CASE-Association/FolkraceCar/img/Stream/img1.jpg

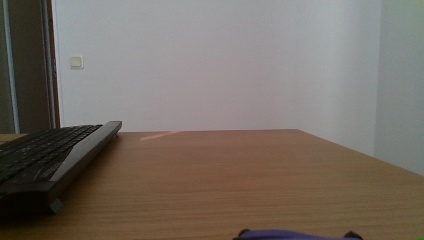
img/Stream/img1.jpg
