CASE-Association/FolkraceCar/img/Stream/img2.jpg

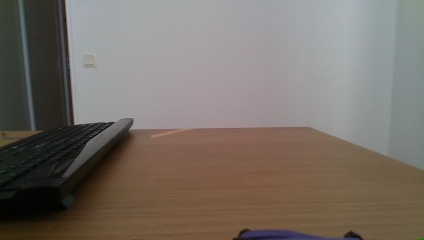
img/Stream/img2.jpg
