CASE-Association/FolkraceCar/img/Stream/img3.jpg

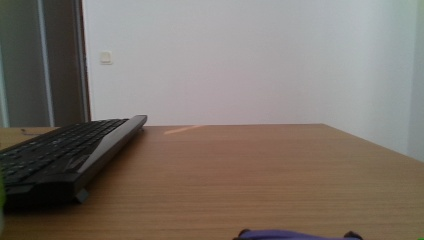
img/Stream/img3.jpg
