CASE-Association/FolkraceCar/img/Stream/img4.jpg

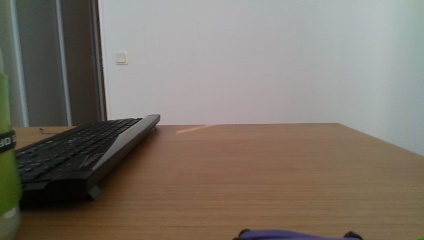
img/Stream/img4.jpg
