CASE-Association/FolkraceCar/img/Stream/img5.jpg

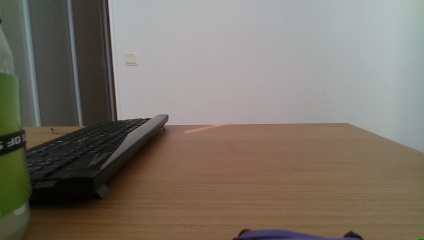
img/Stream/img5.jpg
