CASE-Association/FolkraceCar/img/Stream/img6.jpg

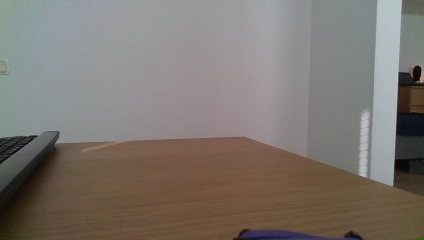
img/Stream/img6.jpg
