CASE-Association/FolkraceCar/img/Stream/img7.jpg

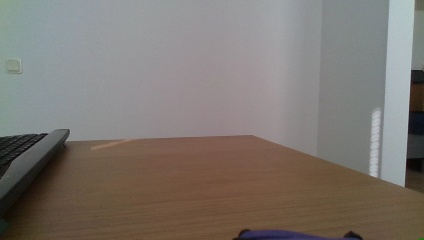
img/Stream/img7.jpg
