CASE-Association/FolkraceCar/img/Stream/img8.jpg

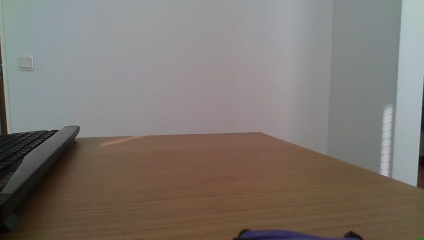
img/Stream/img8.jpg
