CASE-Association/FolkraceCar/img/Stream/img9.jpg

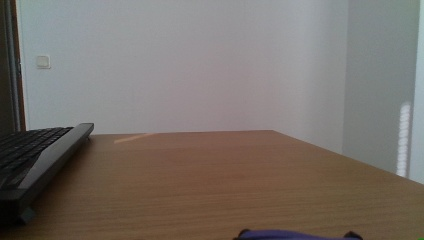
img/Stream/img9.jpg
