CASE-Association/FolkraceCar/software/module/pathplanner.py

from numpy.linalg import svd, det
import multiprocessing as mp
from module.camera import *
import numpy as np
from threading import Thread
import module.config as conf


class PathFinder:
    def __init__(self, car):

        self.cam = None
        self._car = car
        self._camera_offset = self._car.size[2] - self._car.camera_offset[2]

        self.verts = None
        self.ground_plane = None #  self._get_ground_plane()

        # Path planning variables
        self.theta = 0.0  # steering direction
        self.phi = 0.0  # incline angle
        self.dist = -1.0  # distance to object
        self.t_last_data = 0.0  # last valid data reading
        self.samplerate = 0.0
        self.fov = conf.FOV  # FieldOfView
        self.q = mp.Queue()  # message queue

        self.pp = None

    def start(self):
        """
        Start path planner as own process
        :return: Pathplanner process
        """
        self.pp = mp.Process(target=self.run, name='path_planner', args=(self.q,))
        try:
           self.pp.start()
        except Exception as err:
            print("Error: unable to start path_planner thread, err: {}".format(err))
        return self.pp

    def end(self):
        """
        end Pathplanner process
        :return: process exitcode
        """
        self.q.put("END")
        if self.pp.is_alive():
            self.pp.join(timeout=1)
        self.q.close()
        self.q.join_thread()
        if self.pp.is_alive:
            self.pp.terminate()
            print('\n\033[91m Path planner terminated\033[0m')
        else:
            print('\n\033[92m Path planner ended\033[0m')
        return self.pp.exitcode

    def _rigid_transform_3D(self, A, B):
        assert len(A) == len(B)

        N = A.shape[0]  # total points

        centroid_A = np.mean(A, axis=0)
        centroid_B = np.mean(B, axis=0)

        # centre the points
        AA = A - np.tile(centroid_A, (N, 1))
        BB = B - np.tile(centroid_B, (N, 1))

        # dot is matrix multiplication for array
        H = np.transpose(AA) * BB

        U, S, Vt = svd(H)

        R = Vt.T * U.T

        # special reflection case
        if det(R) < 0:
            Vt[2, :] *= -1
            R = Vt.T * U.T

        t = -R * centroid_A.T + centroid_B.T

        return R, t

    def _get_ground_plane(self):
        """
        Estimate ground plain using Least square
        :return: groudn plain origin and rotation
        """

        pos, normal = self._planeFit()

        rot, _ = self._rigid_transform_3D(pos, normal)

        rot = np.eye(3)  # todo calculate rotation matrix

        return pos, rot, normal

    def _planeFit(self):
        """
        Original code from: https://stackoverflow.com/a/18968498

        p, n = planeFit(points)

        Given an array, points, of shape (d,...)
        representing points in d-dimensional space,
        fit an d-dimensional plane to the points.

        :return: a point, p, on the plane (the point-cloud centroid),
        and the normal, n.
        """

        verts_t = np.transpose(self.verts)

        verts_t = np.reshape(verts_t, (np.shape(verts_t)[0], -1))  # Collapse trialing dimensions
        assert verts_t.shape[0] <= verts_t.shape[1], "There are only {} points in {} dimensions.".format(verts_t.shape[1],
                                                                                                       verts_t.shape[0])
        ctr = verts_t.mean(axis=1)
        x = verts_t - ctr[:, np.newaxis]
        M = np.dot(x, x.T)  # Could also use np.cov(x) here.
        return ctr, svd(M)[0][:, -1]

    def _process_verts(self, verts, tunnel_size, theta=0.0, phi=0.0):
        """
        Process verts from Camera.

        :param tunnel_size: the desired tunnel size, [w, h]
        :param theta: The desired turning angle
        :param phi: The desired incline angle.
        :param ground_plane: The estimated driving plane.
        :return: All inlier points in defined direction and for the defined tunnel size.
        """
        # todo
        #  driving plane -> phi angle

        p = verts
        [w, h, l] = tunnel_size
        z_lim = l  # todo get lim from car size like:
        # z_lim = self._camera_offset

        X, Y, Z = p[:, 0], p[:, 1], p[:, 2]

        # inlier index vector
        # I = []

        """
        Basic depth filter (Z)
        do not allow points within car area.
        """

        I = np.where((Z > z_lim))[0]
        # if no inliers return None
        if not I.any():
            return None

        """
        Filter height (Y) inliers    # todo implement plane filter instead of static height
        
        using the line equation y = kx + m we can  formulate the inlier constraint as
        -mlim <= m <= mlim for m = y - kx. 
        In this case we substitute y with the Y-array (Height) and x with the Z - array (Depth).  
        """
        radPhi = np.deg2rad(phi)
        k_y = np.tan(-radPhi)  # negate to get correct incline direction
        mlim_h = [-h / 2, h / 2]
        m = np.subtract(Y[I], np.multiply(k_y, Z[I]))  # {m = y - kx} => m = Y - k.*Z
        # Inlier indexes
        I_y = np.where(np.logical_and(mlim_h[0] <= m, mlim_h[1] >= m))[0]

        I = I[I_y]

        """
        Filter width (X) inliers 
        
        using the same equation as above but now with the m being a function of k,X and Z.
        we now only use inliers (I_y) form the above step to reduce necessary computations.
        """
        radTheta = np.deg2rad(theta)
        k_x = np.tan(radTheta)
        mlim_w = [-w / 2, w / 2]
        m = np.subtract(X[I], np.multiply(k_x, Z[I]))  # {m = y - kx} => m = X - k.*Z
        # Inlier of Y inliers
        I_x = np.where(np.logical_and(mlim_w[0] <= m, mlim_w[1] >= m))[0]

        # Pop outliers from I
        I = I[I_x]

        return p[I]

    def _get_path(self, alpha=conf.PATH_SMOOTHING):
        """
        Get distance and heading to longest path
        :param alpha: smoothing factor
        :return: None
        """

        # todo:
        #  get theta span depending on furthest distance
        #  weight non-linear path depending on speed
        #  imp max theta and speed change

        theta = None
        tunnel_size = self._car.size[0:3]  # [w h l_offset]
        #self.verts = self.cam.get_verts()
        self.ground_plane = self._get_ground_plane()

        max_dist = 0  # longest found path distance
        n_scan_steps = 15

        for _theta in range(int(self.theta - self.fov / 2), int(self.theta + self.fov / 2 + 1), n_scan_steps):

            # process verts to get inlier points
            inliers = self._process_verts(self.verts, tunnel_size=tunnel_size, theta=_theta, phi=self.phi)
            try:
                Z = inliers[:, 2]
                _dist = np.min(Z)
                if _dist >= max_dist * 1.25:  # Must be more than 25% longer to change heading
                    theta = _theta
                    max_dist = _dist
            except:
                pass

        if theta is not None:
            # Smoothing
            self.theta = alpha * theta + (1 - alpha) * self.theta
            self.dist = min(alpha * max_dist + (1 - alpha) * self.dist, max_dist)

    def _image_extraction(self):
        """
        Image extraction thread
        :return: None
        """
        # todo move to thread in Camera class
        try:
            while True:
                shared.raw_image = shared.nparray_to_rawarray(self.cam.get_image())
                shared.t_raw_image.value = time.perf_counter()
        except Exception as err:
            print('Error in image extraction thread: ', err)

    def run(self, q):
        """
        Main Path planner Process
        :param q: message queue
        :return: none
        """
        rx_msg = tx_msg = []

        # Init RealSense camera with threading
        self.cam = init_camera()

        # If Raw image is requested, start tread for image extraction
        if conf.IMAGERAW:
            ie = Thread(target=self._image_extraction)
            #ie.daemon = True
            ie.start()

        while True:
            # get RX data from queue
            # todo

            # get verts from camera
            self.verts = self.cam.get_verts()

            # Get sample rate
            _t_now = time.perf_counter()
            self.samplerate = 1 / (_t_now - self.t_last_data)
            self.t_last_data = _t_now

            # Get new path
            self._get_path()

            # Create TX message
            tx_msg = {'dist': self.dist,
                      'rate': self.samplerate,
                      'theta': self.theta,
                      'ground': self.ground_plane,
                      'last_reading': self.t_last_data}

            # Check if END command form RX data else send new TX data
            if "END" in rx_msg:
                break  # End process
            elif tx_msg:
                q.put(tx_msg)  # send data as Queue message

        # End process
        while not q.empty():  # flush queue
            q.get()
            time.sleep(0.01)
        q.close()
        self.cam.end()
        print('\n\033[92m Path planner ended\033[0m')
